Panduza/pza-dev-voxpower-inhibiter/PCB_Shield/Arduino_Uno.kicad_sch

## KiCad design PCB_Shield/Arduino_Uno.kicad_sch (2024-07-23)

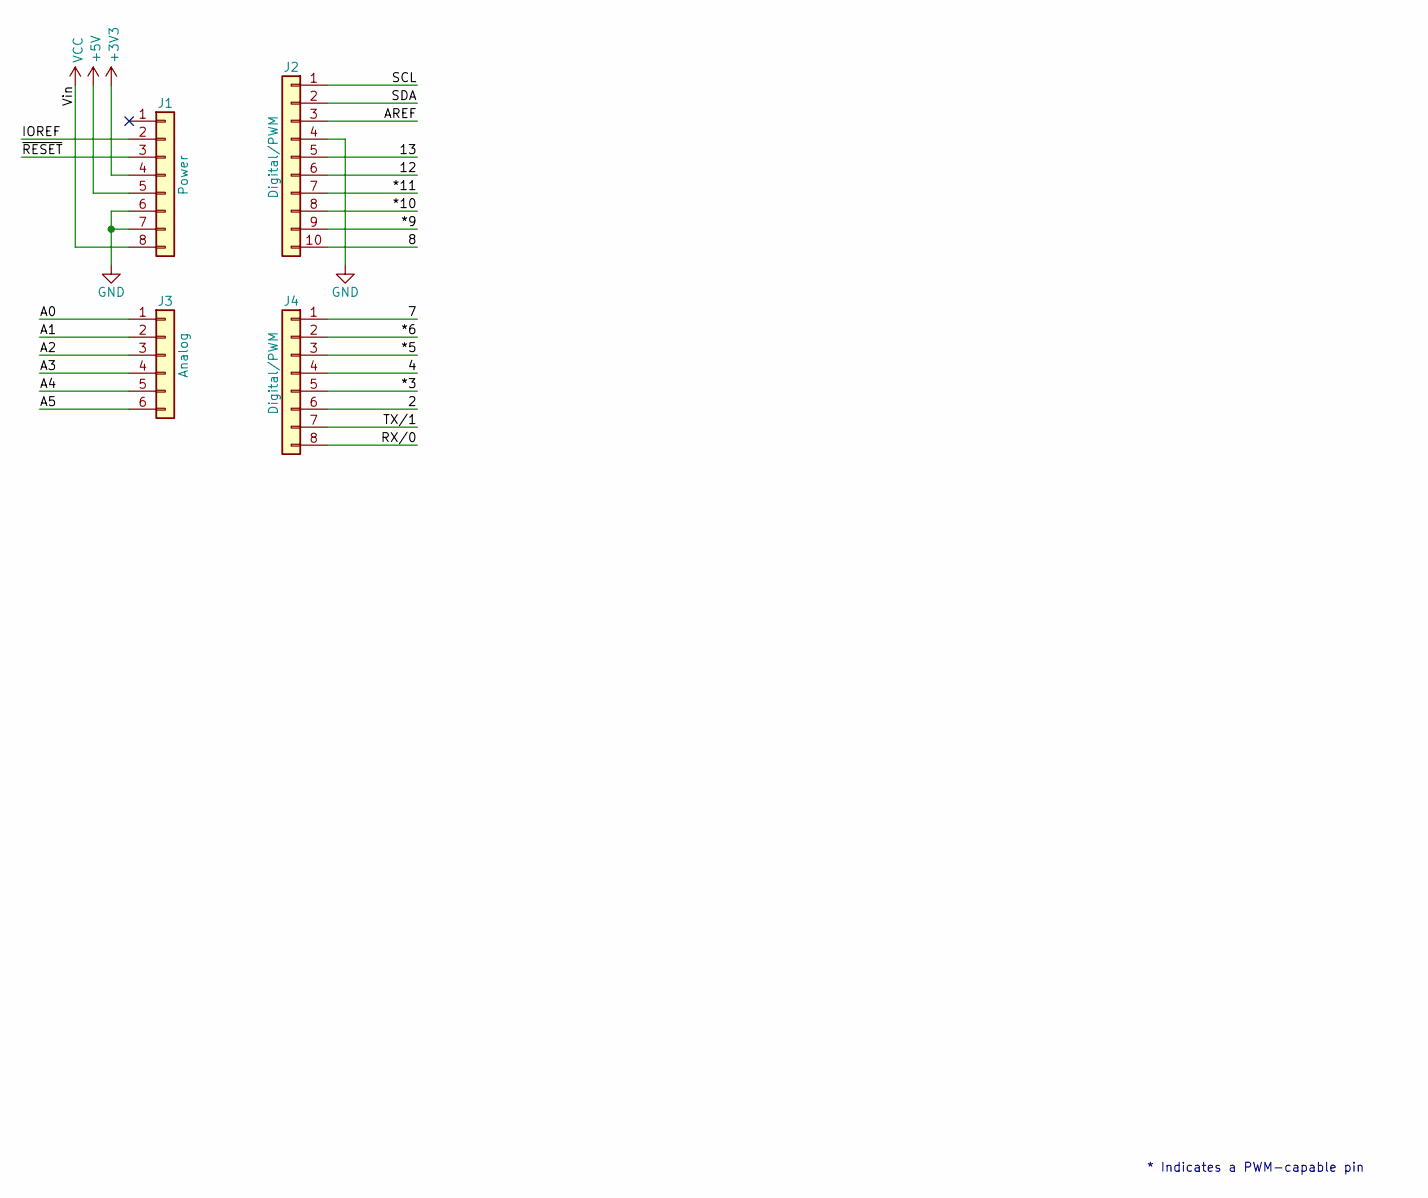
[picture p6: schematic Arduino_Uno.kicad_sch]

Parts:
J1: Power; PinSocket_1x08_P2.54mm_Vertical
J2: Digital/PWM; PinSocket_1x10_P2.54mm_Vertical
J3: Analog; PinSocket_1x06_P2.54mm_Vertical
J4: Digital/PWM; PinSocket_1x08_P2.54mm_Vertical

Connections:
2: J4.6
3: J4.5
4: J4.4
5: J4.3
6: J4.2
7: J4.1
8: J2.10
9: J2.9
10: J2.8
11: J2.7
12: J2.6
13: J2.5
+3V3: J1.4
+5V: J1.5
A0: J3.1
A1: J3.2
A2: J3.3
A3: J3.4
A4: J3.5
A5: J3.6
AREF: J2.3
GND: J1.6, J1.7, J2.4
IOREF: J1.2
RX/0: J4.8
SCL: J2.1
SDA: J2.2
TX/1: J4.7
VCC: J1.8
~RESET: J1.3

Notes on the sheet:
* Indicates a PWM-capable pin
